yehudawe/AirCube/firmware/main/button.c

/**
 * @file button.c
 * @brief Button control for brightness toggling
 * 
 * This file implements button functionality to toggle LED brightness levels.
 * The button is on GPIO 11, normally pulled low and goes high when pressed.
 * 
 * @author StuckAtPrototype, LLC
 * @version 1.0
 */

#include "button.h"
#include "led.h"
#include "zigbee.h"
#include "driver/gpio.h"
#include "esp_log.h"
#include "nvs_flash.h"
#include "nvs.h"
#include "freertos/FreeRTOS.h"
#include "freertos/task.h"
#include "freertos/queue.h"
#include <stdbool.h>

static const char *TAG = "button";

#include "board_config.h"

// Debounce timing (in milliseconds)
#define DEBOUNCE_MS 50

// Long press threshold for Zigbee pairing (in milliseconds)
#define LONG_PRESS_MS 3000

/* Words; 2048 was too small for zigbee_start_pairing() + esp_zb_lock stack use. */
#define BUTTON_TASK_STACK_WORDS 4096

// NVS namespace and key for brightness storage
#define NVS_NAMESPACE "aircube"
#define NVS_KEY_BRIGHTNESS "led_brightness"

// Brightness levels array
static const float brightness_levels[] = {0.0f, 0.1f, 0.3f, 0.6f, 1.0f};
static const int num_brightness_levels = sizeof(brightness_levels) / sizeof(brightness_levels[0]);

// Current brightness index (starts at 0.6, which is index 3)
static int current_brightness_index = 3;  // 0.6 is the default

// GPIO interrupt queue
static QueueHandle_t gpio_evt_queue = NULL;

/**
 * @brief Save brightness index to NVS
 * 
 * @param brightness_index Index of brightness level to save
 * @return true on success, false on failure
 */
static bool save_brightness_to_nvs(int brightness_index)
{
    nvs_handle_t nvs_handle;
    esp_err_t err = nvs_open(NVS_NAMESPACE, NVS_READWRITE, &nvs_handle);
    if (err != ESP_OK) {
        ESP_LOGE(TAG, "Error opening NVS handle: %s", esp_err_to_name(err));
        return false;
    }
    
    err = nvs_set_i32(nvs_handle, NVS_KEY_BRIGHTNESS, brightness_index);
    if (err != ESP_OK) {
        ESP_LOGE(TAG, "Error saving brightness to NVS: %s", esp_err_to_name(err));
        nvs_close(nvs_handle);
        return false;
    }
    
    err = nvs_commit(nvs_handle);
    if (err != ESP_OK) {
        ESP_LOGE(TAG, "Error committing NVS: %s", esp_err_to_name(err));
        nvs_close(nvs_handle);
        return false;
    }
    
    nvs_close(nvs_handle);
    ESP_LOGI(TAG, "Brightness saved to NVS: index %d (%.1f)", brightness_index, brightness_levels[brightness_index]);
    return true;
}

/**
 * @brief Load brightness index from NVS
 * 
 * @param brightness_index Pointer to store the loaded brightness index
 * @return true if value was loaded, false if not found or error
 */
static bool load_brightness_from_nvs(int *brightness_index)
{
    nvs_handle_t nvs_handle;
    esp_err_t err = nvs_open(NVS_NAMESPACE, NVS_READONLY, &nvs_handle);
    if (err != ESP_OK) {
        ESP_LOGW(TAG, "Error opening NVS handle: %s (using default)", esp_err_to_name(err));
        return false;
    }
    
    int32_t saved_index = 3; // Default index (0.6)
    err = nvs_get_i32(nvs_handle, NVS_KEY_BRIGHTNESS, &saved_index);
    if (err == ESP_ERR_NVS_NOT_FOUND) {
        ESP_LOGI(TAG, "No saved brightness found in NVS, using default");
        nvs_close(nvs_handle);
        return false;
    } else if (err != ESP_OK) {
        ESP_LOGE(TAG, "Error reading brightness from NVS: %s", esp_err_to_name(err));
        nvs_close(nvs_handle);
        return false;
    }
    
    // Validate the saved index
    if (saved_index < 0 || saved_index >= num_brightness_levels) {
        ESP_LOGW(TAG, "Invalid brightness index %ld in NVS, using default", saved_index);
        nvs_close(nvs_handle);
        return false;
    }
    
    *brightness_index = (int)saved_index;
    nvs_close(nvs_handle);
    ESP_LOGI(TAG, "Brightness loaded from NVS: index %d (%.1f)", *brightness_index, brightness_levels[*brightness_index]);
    return true;
}

/**
 * @brief GPIO interrupt handler
 * 
 * This ISR is called when a GPIO interrupt occurs.
 * It sends the GPIO number to the queue for processing.
 */
static void IRAM_ATTR gpio_isr_handler(void* arg)
{
    uint32_t gpio_num = (uint32_t) arg;
    xQueueSendFromISR(gpio_evt_queue, &gpio_num, NULL);
}

/**
 * @brief Button task to handle debouncing, brightness toggling, and Zigbee pairing
 * 
 * Short press (< 3 s): cycles through brightness levels 0.0 -> 0.1 -> 0.3 -> 0.6 -> 1.0 -> 0.0
 * Long  press (>= 3 s): triggers Zigbee network steering (pairing mode)
 */
static void button_task(void *pvParameters)
{
    uint32_t io_num;
    TickType_t last_press_time = 0;
    
    ESP_LOGI(TAG, "Button task started");
    
    while (1) {
        // Wait for GPIO event from ISR
        if (xQueueReceive(gpio_evt_queue, &io_num, portMAX_DELAY)) {
            TickType_t current_time = xTaskGetTickCount();
            
            // Debounce: only process if enough time has passed since last press
            if (current_time - last_press_time > pdMS_TO_TICKS(DEBOUNCE_MS)) {
                // Verify button is still pressed (debounce check)
                int level = gpio_get_level(io_num);
                if (level == 1) {
                    last_press_time = current_time;
                    
                    // Measure how long the button is held
                    TickType_t press_start = xTaskGetTickCount();
                    bool long_press = false;
                    
                    while (gpio_get_level(io_num) == 1) {
                        vTaskDelay(pdMS_TO_TICKS(50));
                        if ((xTaskGetTickCount() - press_start) >= pdMS_TO_TICKS(LONG_PRESS_MS)) {
                            long_press = true;
                            break;
                        }
                    }
                    
                    if (long_press) {
                        // ── Long press: start Zigbee pairing ──
                        ESP_LOGI(TAG, "Long press detected – starting Zigbee pairing");
                        zigbee_start_pairing();
                        
                        // Wait for button release before accepting new events
                        while (gpio_get_level(io_num) == 1) {
                            vTaskDelay(pdMS_TO_TICKS(50));
                        }
                        
                        // Drain any queued events accumulated during the hold
                        while (xQueueReceive(gpio_evt_queue, &io_num, 0) == pdTRUE) {}
                    } else {
                        // ── Short press: cycle brightness ──
                        current_brightness_index = (current_brightness_index + 1) % num_brightness_levels;
                        float new_brightness = brightness_levels[current_brightness_index];
                        
                        led_set_intensity(new_brightness);
                        save_brightness_to_nvs(current_brightness_index);
                        zigbee_report_brightness();

                        ESP_LOGI(TAG, "Short press – Brightness set to %.1f", new_brightness);
                    }
                }
            }
        }
    }
}

/**
 * @brief Initialize button functionality
 * 
 * This function configures GPIO 11 as an input with pull-down resistor
 * and sets up an interrupt on rising edge (button press).
 */
void button_init(void)
{
    ESP_LOGI(TAG, "Initializing button on GPIO %d", BUTTON_GPIO);
    
    // Create queue for GPIO events
    gpio_evt_queue = xQueueCreate(10, sizeof(uint32_t));
    if (gpio_evt_queue == NULL) {
        ESP_LOGE(TAG, "Failed to create GPIO event queue");
        return;
    }
    
    // Configure GPIO
    gpio_config_t io_conf = {
        .intr_type = GPIO_INTR_POSEDGE,      // Interrupt on rising edge (LOW -> HIGH)
        .mode = GPIO_MODE_INPUT,              // Input mode
        .pin_bit_mask = (1ULL << BUTTON_GPIO), // GPIO 11
        .pull_down_en = GPIO_PULLDOWN_ENABLE, // Enable pull-down (button normally LOW)
        .pull_up_en = GPIO_PULLUP_DISABLE,    // Disable pull-up
    };
    
    esp_err_t ret = gpio_config(&io_conf);
    if (ret != ESP_OK) {
        ESP_LOGE(TAG, "Failed to configure GPIO: %s", esp_err_to_name(ret));
        return;
    }
    
    // Install GPIO ISR service
    ret = gpio_install_isr_service(0);
    if (ret != ESP_OK && ret != ESP_ERR_INVALID_STATE) {
        // ESP_ERR_INVALID_STATE means ISR service already installed (OK)
        ESP_LOGE(TAG, "Failed to install GPIO ISR service: %s", esp_err_to_name(ret));
        return;
    }
    
    // Hook ISR handler for specific GPIO
    ret = gpio_isr_handler_add(BUTTON_GPIO, gpio_isr_handler, (void*) BUTTON_GPIO);
    if (ret != ESP_OK) {
        ESP_LOGE(TAG, "Failed to add ISR handler: %s", esp_err_to_name(ret));
        return;
    }
    
    // Create button task
    BaseType_t task_ret = xTaskCreate(button_task, "button_task", BUTTON_TASK_STACK_WORDS, NULL, 5, NULL);
    if (task_ret != pdPASS) {
        ESP_LOGE(TAG, "Failed to create button task");
        return;
    }
    
    // Load saved brightness from NVS, or use default
    int saved_index = 3; // Default index (0.6)
    if (load_brightness_from_nvs(&saved_index)) {
        current_brightness_index = saved_index;
    }
    
    // Set initial brightness (either from NVS or default)
    led_set_intensity(brightness_levels[current_brightness_index]);
    
    ESP_LOGI(TAG, "Button initialized successfully");
}
